codepainters/lvov/orig/keyboard_pcb.jpg

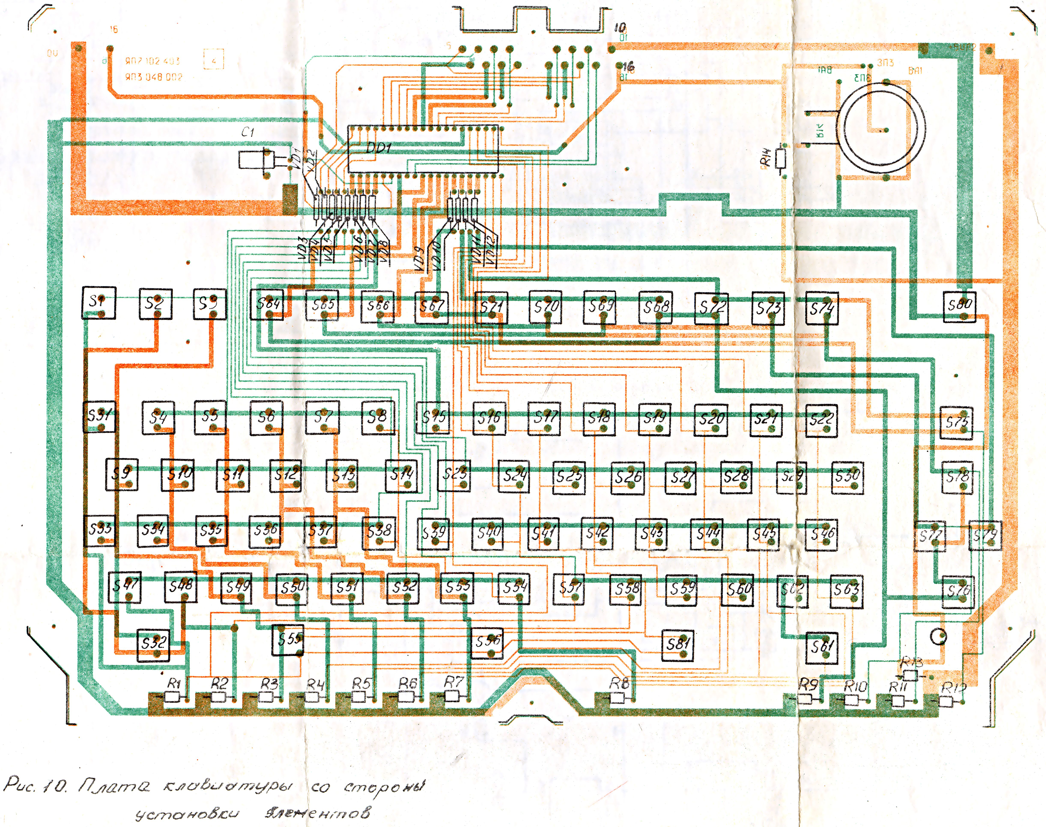
orig/keyboard_pcb.jpg
