codepainters/lvov/orig/psu_pcb.jpg

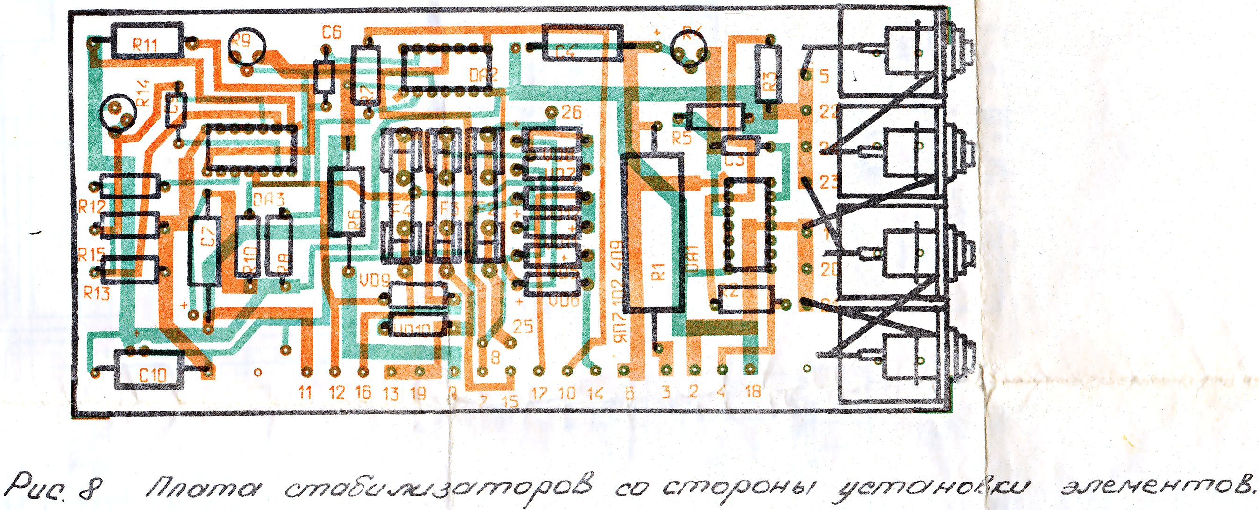
orig/psu_pcb.jpg
