codepainters/lvov/sch/lviv.kicad_pcb

## KiCad design ecad/ohmcontrol/ohmcontrol.kicad_sch

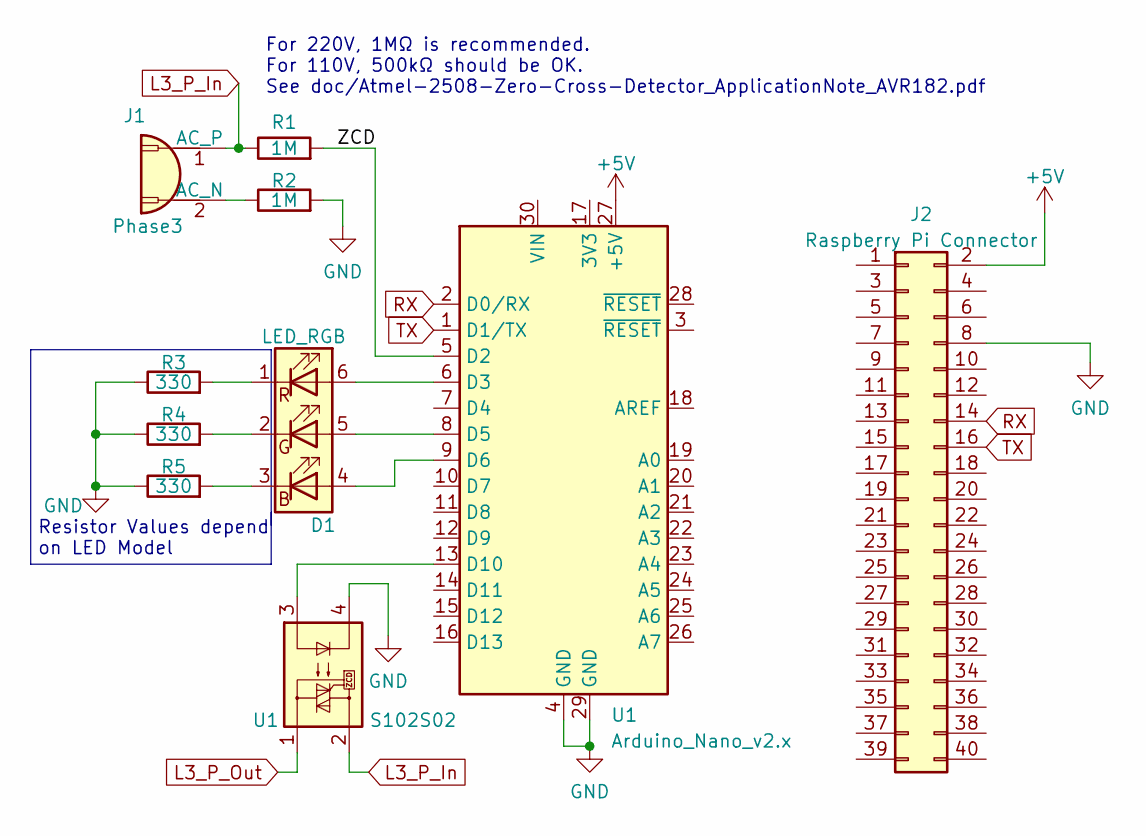
[picture p43: schematic ohmcontrol.kicad_sch]

Parts:
D1: LED_RGB
J1: Phase3
J2: Raspberry Pi Connector
R1, R2: 1M
R3, R4, R5: 330
U1: S102S02; SIP4_Sharp-SSR_P7.62mm_Straight

Connections:
+5V: J2.2, U1.27 (+5V)
GND: J2.8, R2.2, R3.1, R4.1, R5.1, U1.4 (GND), U1.29 (GND)
L3_P_In: J1.1 (AC_P), R1.1, U1.2 (D0/RX)
L3_P_Out: U1.1 (D1/TX)
unnamed: D1.1 (RK), R3.2
unnamed: D1.2 (GK), R4.2
unnamed: D1.3 (BK), R5.2
unnamed: D1.4 (BA), U1.9 (D6)
unnamed: D1.5 (GA), U1.8 (D5)
unnamed: D1.6 (RA), U1.6 (D3)
unnamed: J1.2 (AC_N), R2.1
unnamed: U1.3 (~RESET), U1.13 (D10)
RX: J2.14, U1.2 (D0/RX)
TX: J2.16, U1.1 (D1/TX)
ZCD: R1.2, U1.5 (D2)

Notes on the sheet:
For 220V, 1MΩ is recommended. For 110V, 500kΩ should be OK. See doc/Atmel-2508-Zero-Cross-Detector_ApplicationNote_AVR182.pdf
Resistor Values depend on LED Model
